madcatse/Delta-S-M/docs/Datasheets/buzzer_1.jpg

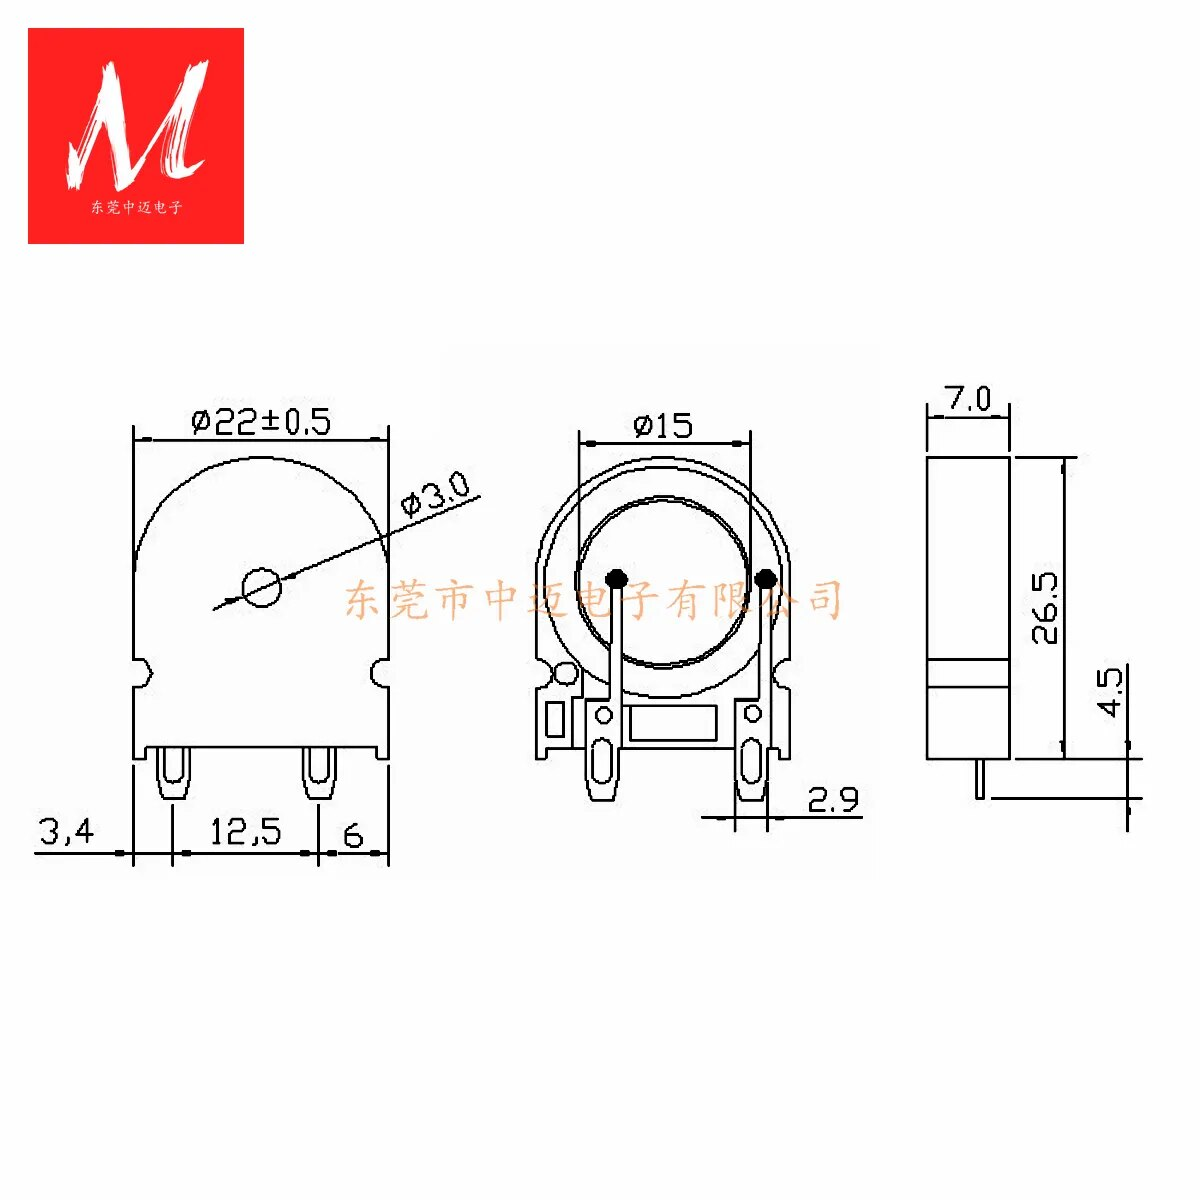
docs/Datasheets/buzzer_1.jpg
