madcatse/Delta-S-M/docs/Original Delta/2023-03-13 20.28.30-min.jpg

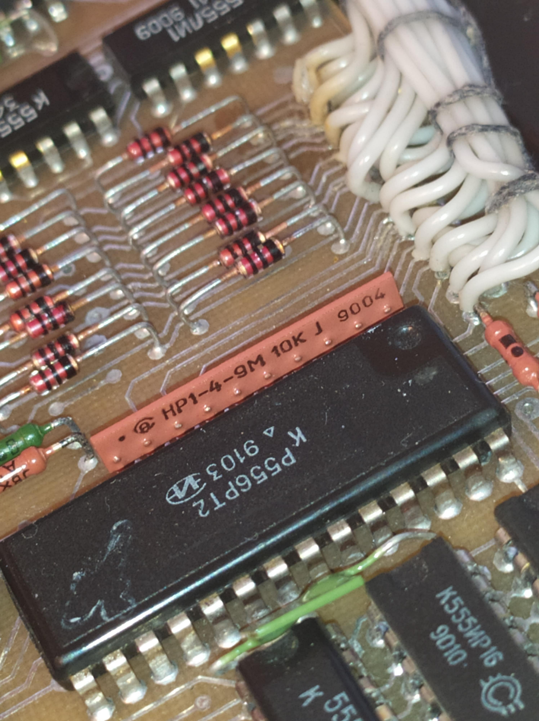
docs/Original Delta/2023-03-13 20.28.30-min.jpg
