madcatse/Delta-S-M/docs/Original Delta/2023-03-13 20.31.33-min.jpg

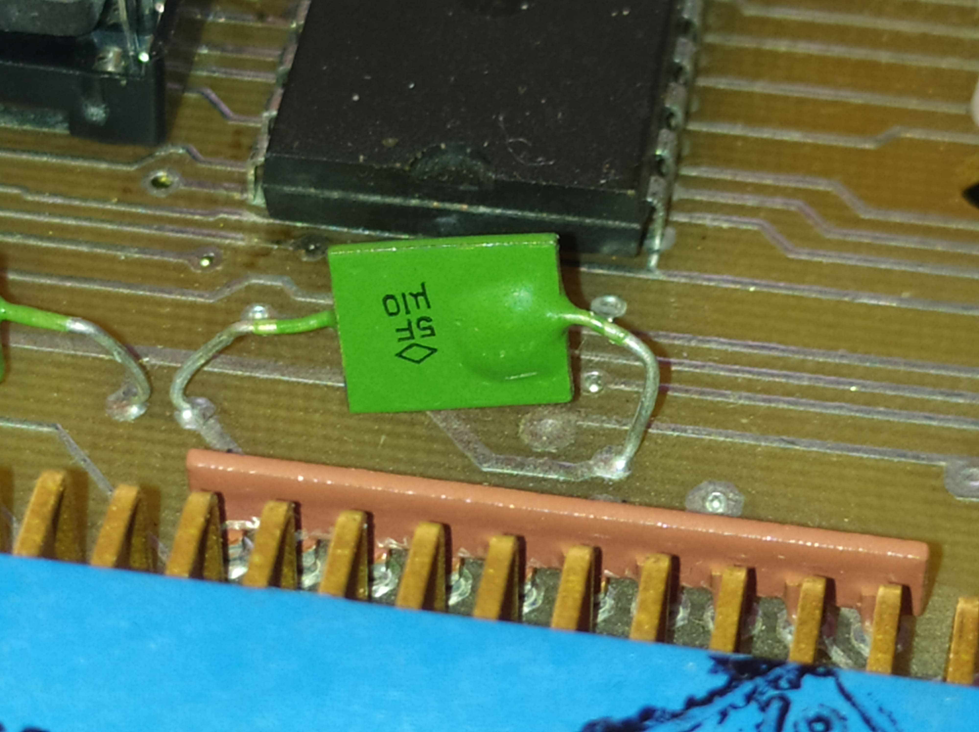
docs/Original Delta/2023-03-13 20.31.33-min.jpg
