madcatse/Delta-S-M/docs/Original Delta/2023-03-17 20.00.24-min.jpg

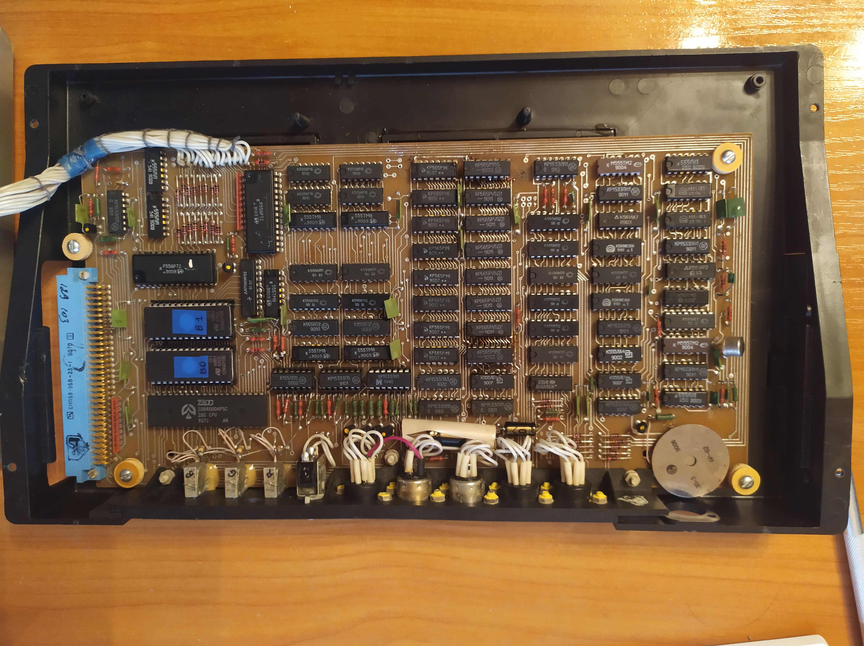
docs/Original Delta/2023-03-17 20.00.24-min.jpg
