madcatse/Delta-S-M/docs/Original Delta/2023-03-26 23.38.39-min.jpg

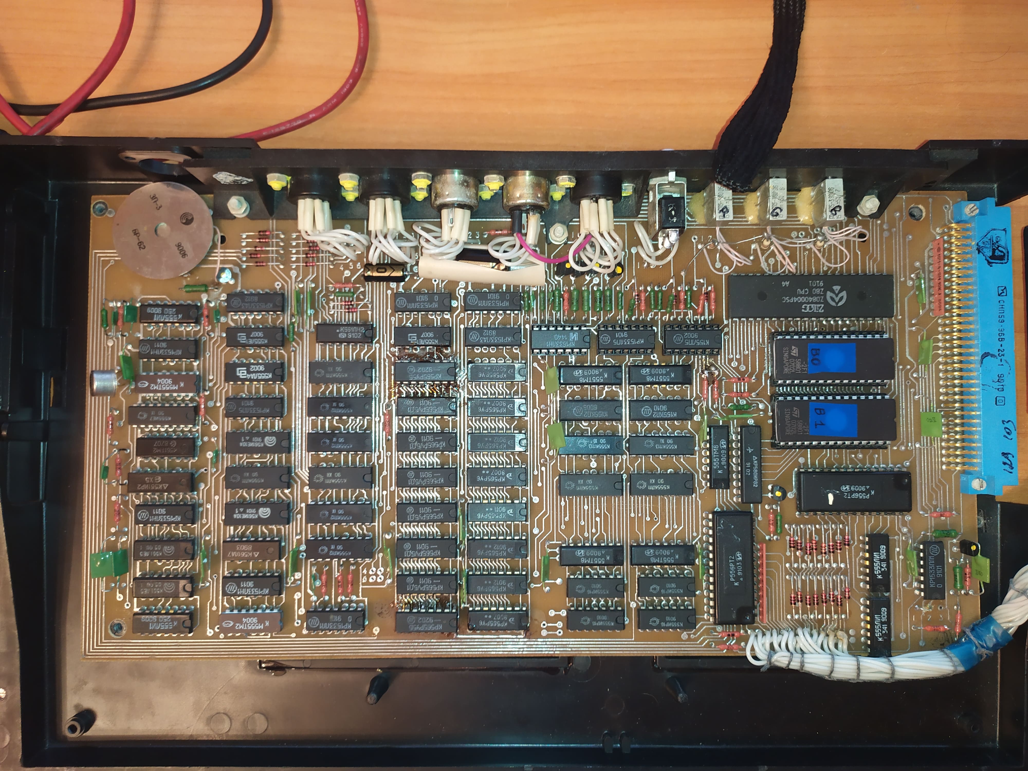
docs/Original Delta/2023-03-26 23.38.39-min.jpg
