madcatse/Delta-S-M/docs/photo_2026-02-04_22-32-54.jpg

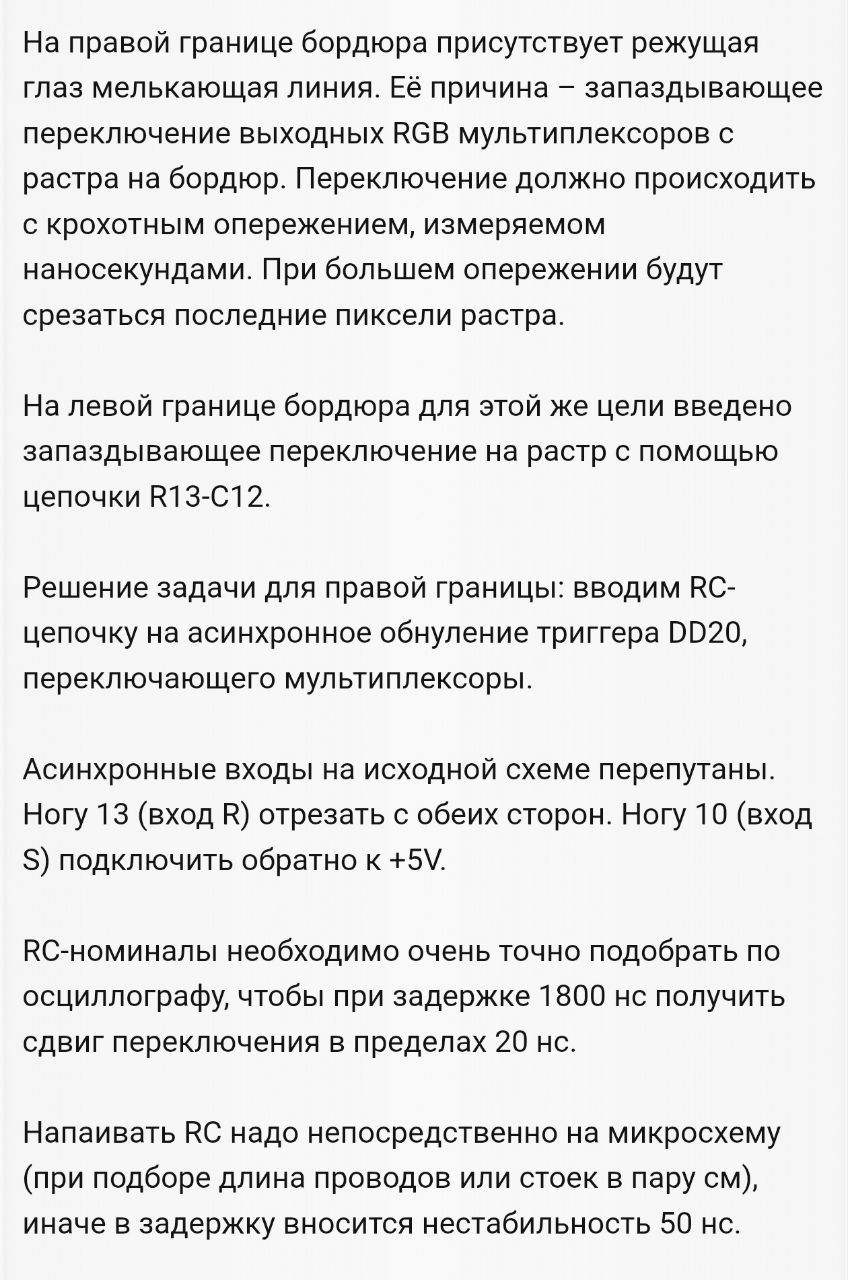
docs/photo_2026-02-04_22-32-54.jpg
