madcatse/Delta-S-M/docs/photo_2026-03-28_18-53-08.jpg

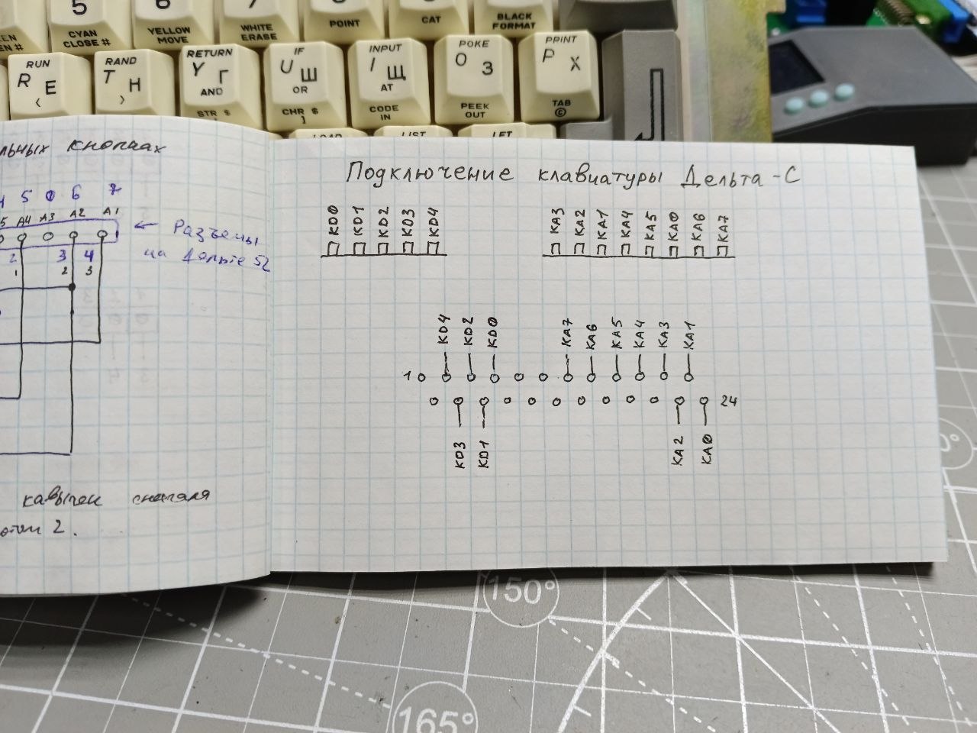
docs/photo_2026-03-28_18-53-08.jpg
