madcatse/Delta-S-M/docs/Photos of dead board/2023-03-13 19.23.34-min.jpg

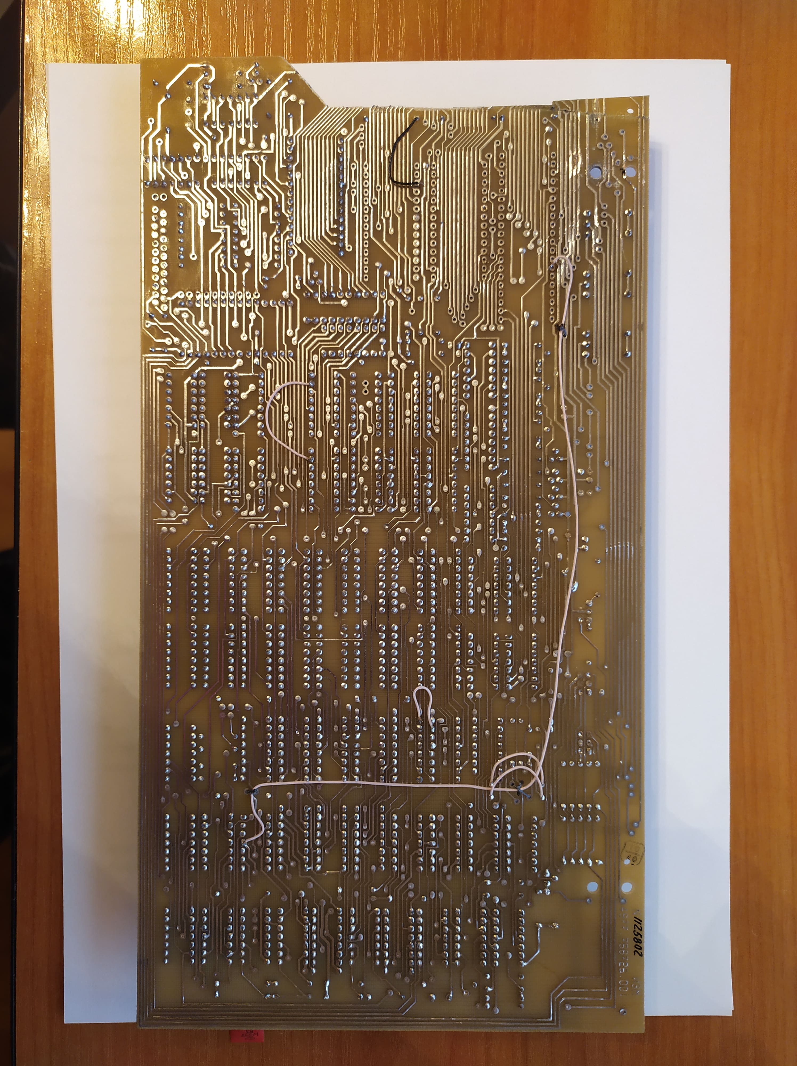
docs/Photos of dead board/2023-03-13 19.23.34-min.jpg
