madcatse/Delta-S-M/keyboard_cherry/ali.jpg

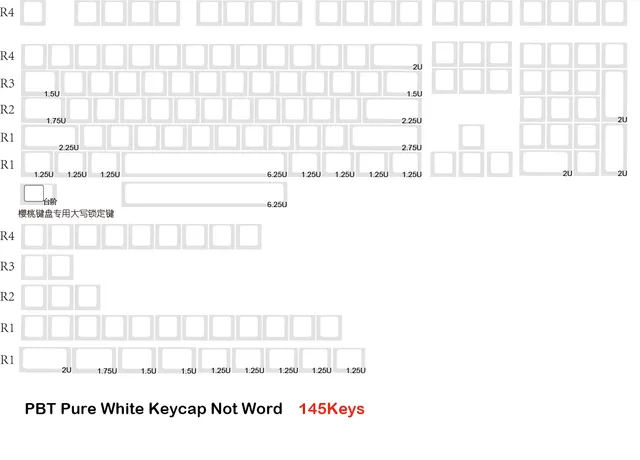
keyboard_cherry/ali.jpg
