madcatse/Delta-S-M/keyboard_cherry/keyboard_layount.jpg

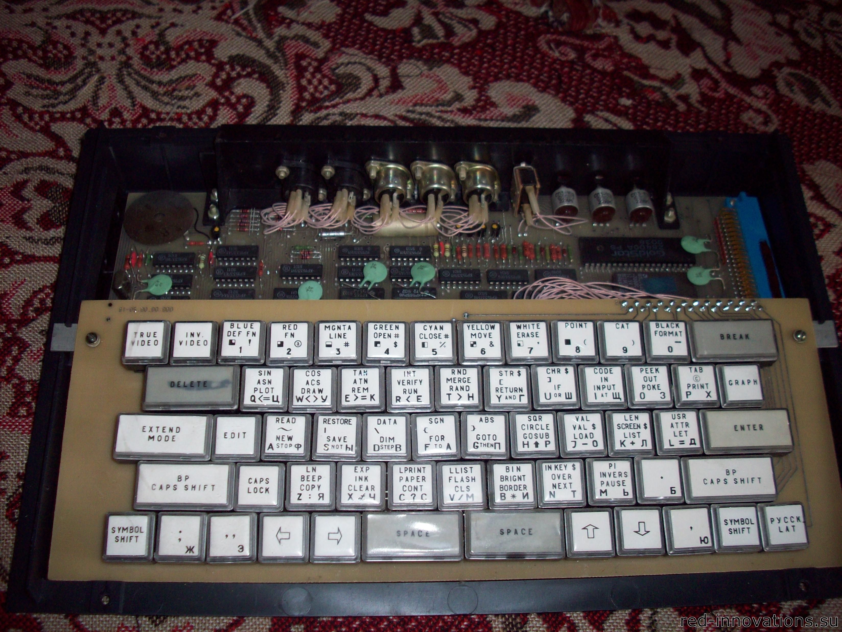
keyboard_cherry/keyboard_layount.jpg
