madcatse/Delta-S-M/keyboard_cherry/New_keyboard_layout.jpg

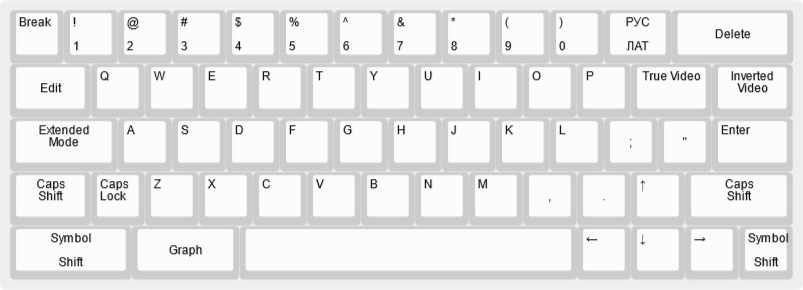
keyboard_cherry/New_keyboard_layout.jpg
