madcatse/Delta-S-M/keyboard_cherry/raw_data/rev2/delta-s-m-rev-2.png

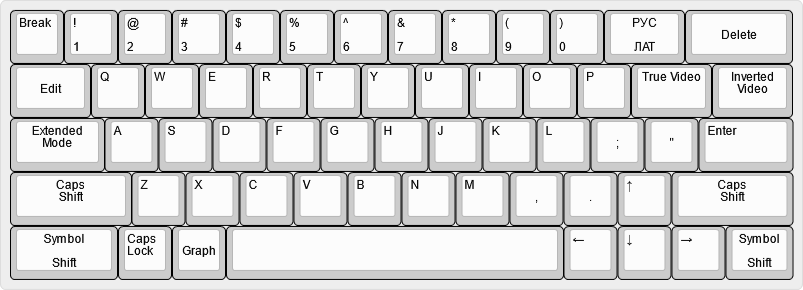
keyboard_cherry/raw_data/rev2/delta-s-m-rev-2.png
