madcatse/Delta-S-M/keyboard_cherry/raw_data/rev2/summary.PNG

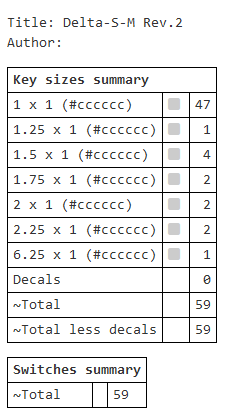
keyboard_cherry/raw_data/rev2/summary.PNG
