madcatse/Delta-S-M/keyboard_cherry/Stabilizer_MX_2.00u.step

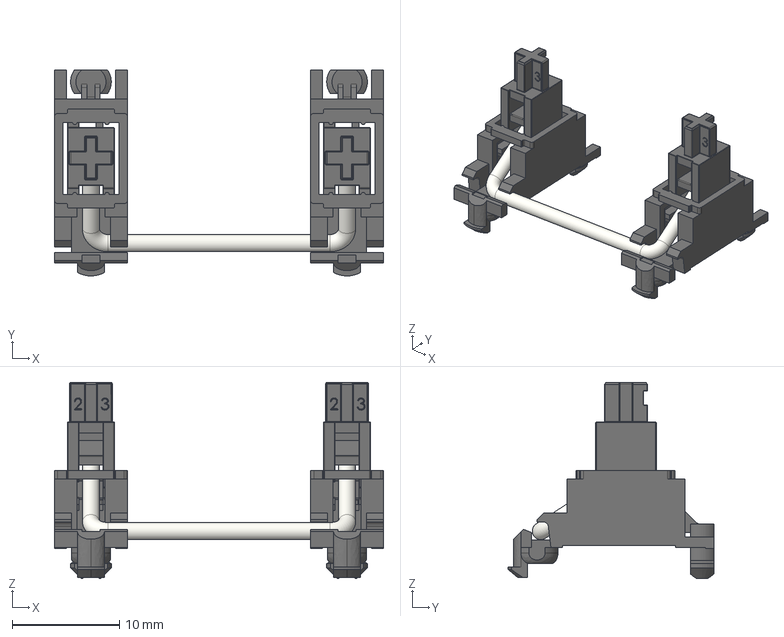
[picture p43: CAD file, 2023-10-09]
keyboard_cherry/Stabilizer_MX_2.00u.step
30.7 x 19.2 x 18.3 mm
