madcatse/Delta-S-M/keyboard_cherry/MX_PCB.step

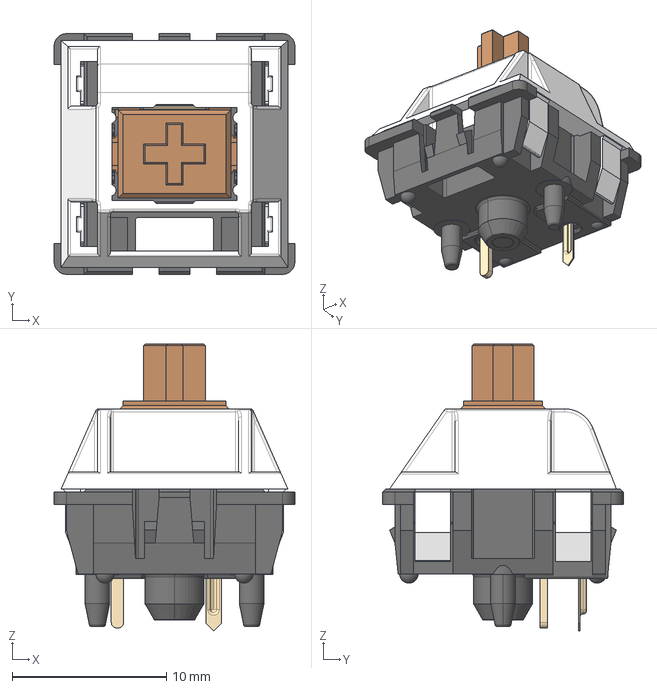
[picture p44: CAD file, 2023-10-09]
keyboard_cherry/MX_PCB.step
15.6 x 15.6 x 18.6 mm
